gianlucag/SidBerry/hardware/Arietta G25/SidBerry_AriettaG25_board3.JPG

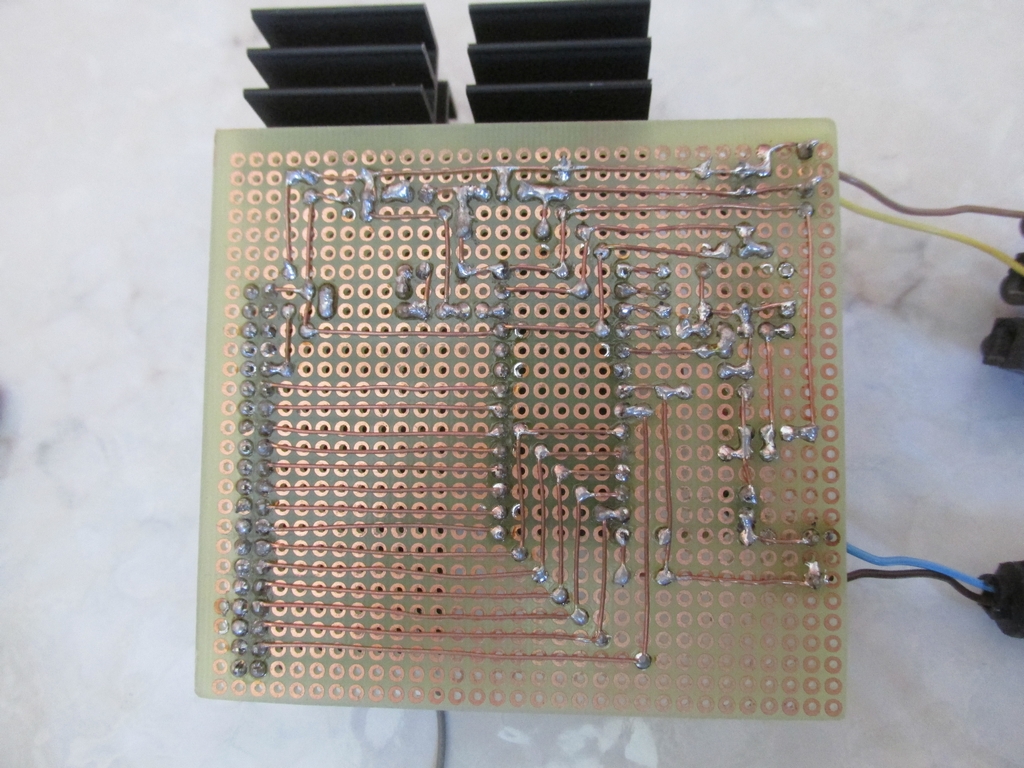
hardware/Arietta G25/SidBerry_AriettaG25_board3.JPG
