gianlucag/SidBerry/hardware/Raspberry Pi/SidBerry_RaspberryPi_by_Thoroide_board1.png

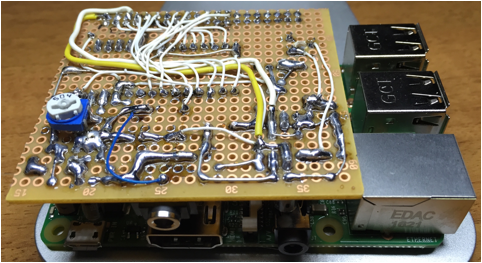
hardware/Raspberry Pi/SidBerry_RaspberryPi_by_Thoroide_board1.png
